JordanAceto/stm32l0_mod_source/docs/html_nav/images/cat_pcb_bottom_jpg_stm32l0_mod_source-bottom.png

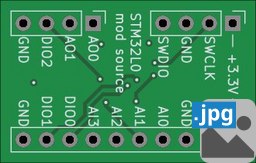
docs/html_nav/images/cat_pcb_bottom_jpg_stm32l0_mod_source-bottom.png
