JordanAceto/stm32l0_mod_source/docs/html_nav/images/cat_pcb_top_jpg_stm32l0_mod_source-top.png

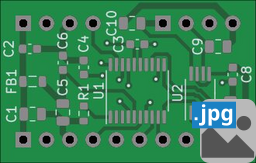
docs/html_nav/images/cat_pcb_top_jpg_stm32l0_mod_source-top.png
