JordanAceto/stm32l0_mod_source/docs/html_nav/images/cat_pdf_layers_stm32l0_mod_source-B_Courtyard.png

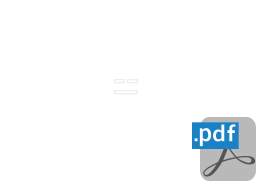
docs/html_nav/images/cat_pdf_layers_stm32l0_mod_source-B_Courtyard.png
