JordanAceto/stm32l0_mod_source/docs/2D/individual_layers/stm32l0_mod_source-F_Fab.pdf

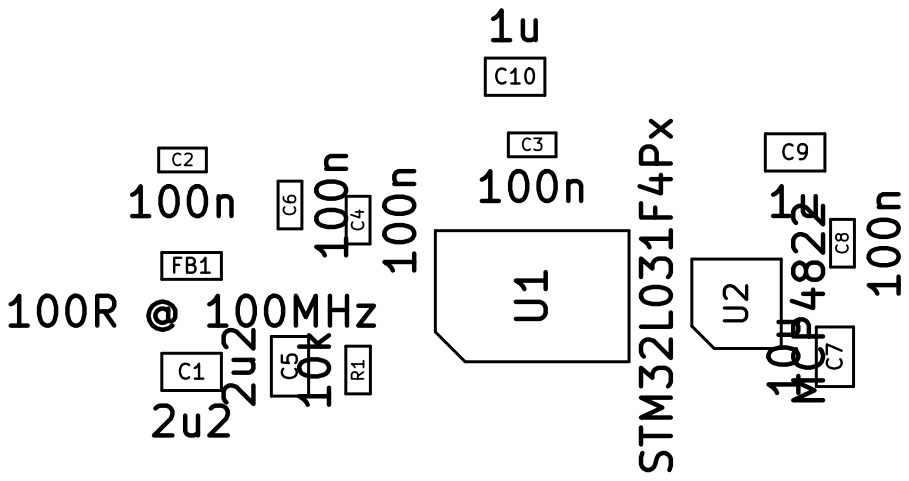
[picture p23: page 1]
