JordanAceto/stm32l0_mod_source/docs/2D/individual_layers/stm32l0_mod_source-F_Mask.pdf

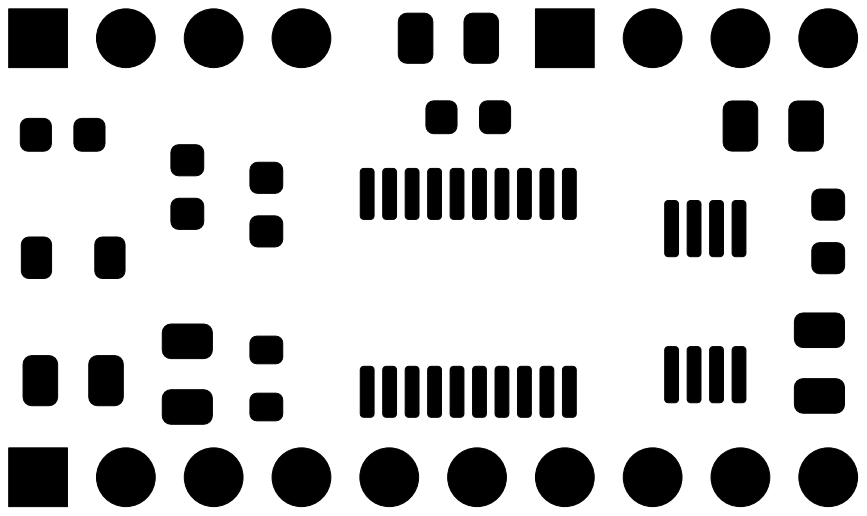
[picture p24: page 1]
