JordanAceto/stm32l0_mod_source/docs/2D/individual_layers/stm32l0_mod_source-F_Silkscreen.pdf

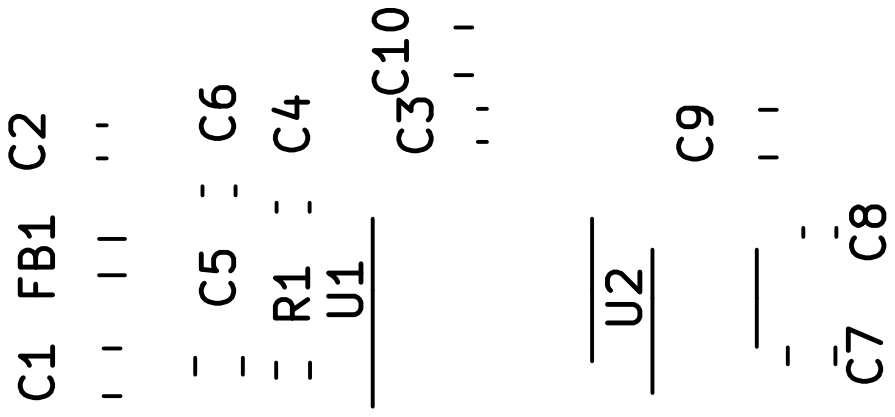
[picture p25: page 1]
