JordanAceto/stm32l0_mod_source/docs/2D/individual_layers/stm32l0_mod_source-In1_Cu.pdf

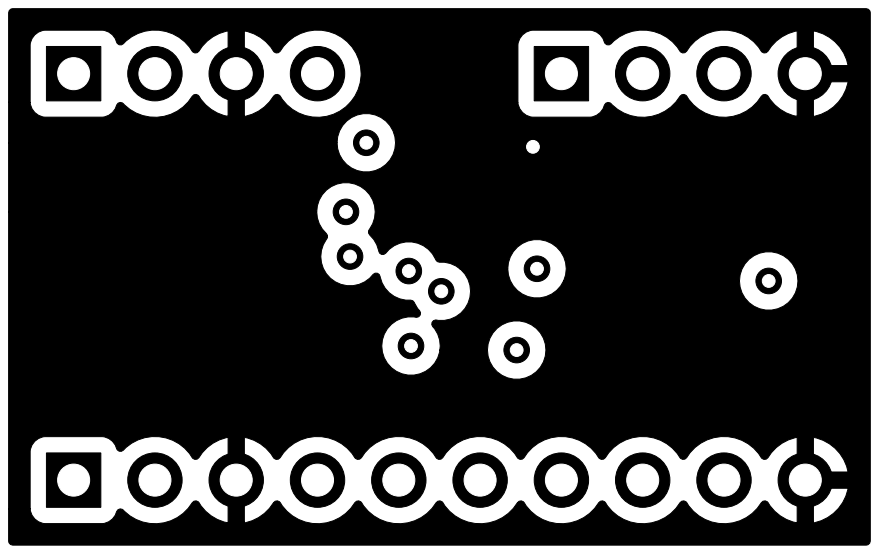
[picture p26: page 1]
