JordanAceto/stm32l0_mod_source/docs/2D/individual_layers/stm32l0_mod_source-In2_Cu.pdf

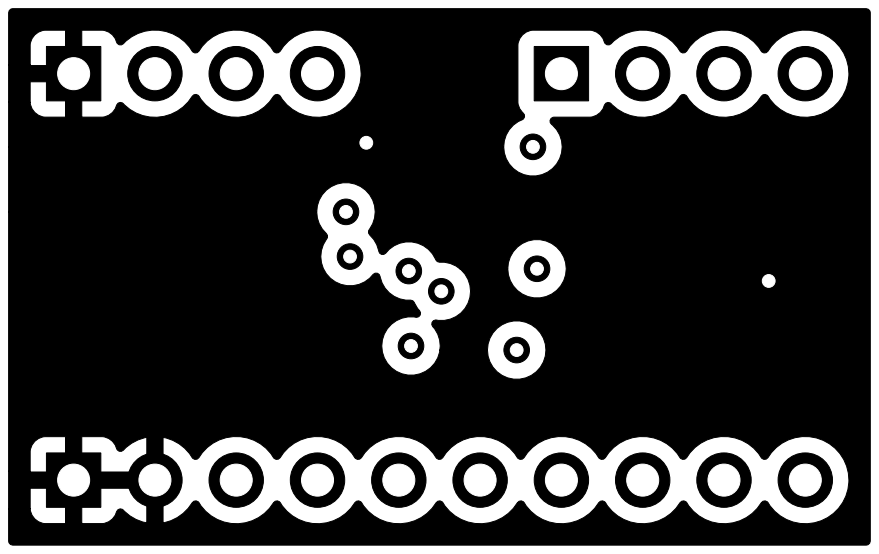
[picture p27: page 1]
