JordanAceto/stm32l0_mod_source/docs/html_nav/images/cat_pdf_pcb_print_BCu_stm32l0_mod_source-B_Cu.png

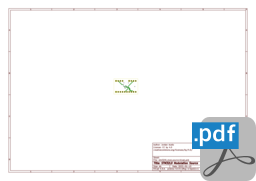
docs/html_nav/images/cat_pdf_pcb_print_BCu_stm32l0_mod_source-B_Cu.png
