JordanAceto/stm32l0_mod_source/docs/html_nav/images/cat_pdf_sch_print_stm32l0_mod_source-schematic.png

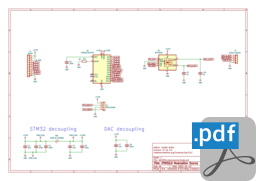
docs/html_nav/images/cat_pdf_sch_print_stm32l0_mod_source-schematic.png
